fonske/Salt-level-tof-atoms3/README/sensor_img_1.jpg

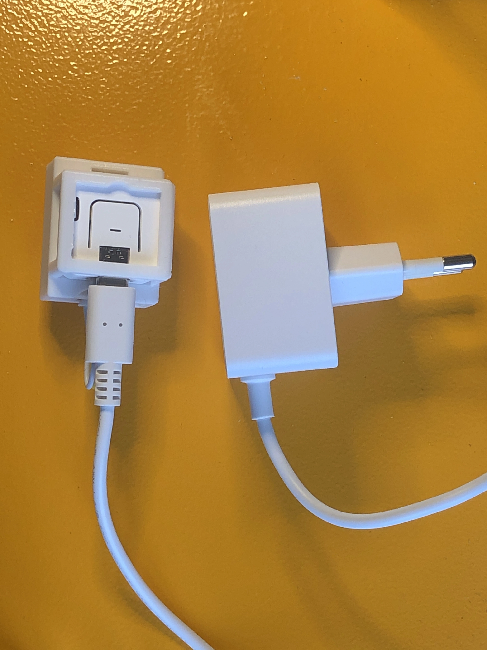
README/sensor_img_1.jpg
